cesargillao/pediluvio-ionico-zapper-pic16f876/Software/asmoutput.asm

0000: 
       GOTO   L00A2
L0001  MOVLW  80h
       MOVWF  21h
       MOVLW  0FEh
       CALL   L0061
       MOVLW  1
       CALL   L0061
       MOVLW  75h
       MOVWF  24h
       MOVLW  30h
       GOTO   L0072
L000B  CLRF   21h
       BSF    21h,7
       MOVWF  2Ch
       MOVLW  0FEh
       CALL   L0061
       MOVF   2Ch,W
       GOTO   L0061
L0012  MOVWF  2Ah
       BCF    6,2
       BCF    6,3
       BSF    3,5
       BCF    6,2
       BCF    6,3
       MOVLW  0Fh
       ANDWF  6,F
       BCF    3,5
       MOVF   2Ah,W
       BTFSC  20h,1
       GOTO   L003C
       MOVLW  3Eh
       MOVWF  24h
       MOVLW  80h
       CALL   L0072
       MOVLW  33h
       MOVWF  29h
       CALL   L0050
       MOVLW  13h
       MOVWF  24h
       MOVLW  88h
       CALL   L0072
       CALL   L0050
       MOVLW  64h
       CALL   L0071
       CALL   L0050
       MOVLW  64h
       CALL   L0071
       MOVLW  22h
       MOVWF  29h
       CALL   L0050
       MOVLW  28h
       CALL   L003B
       MOVLW  0Ch
       CALL   L003B
       MOVLW  6
       CALL   L003B
       BSF    20h,1
       MOVF   2Ah,W
       GOTO   L003C
L003B  BSF    20h,0
L003C  MOVWF  29h
       BTFSS  20h,0
       GOTO   L004A
       BCF    6,3
       SUBLW  3
       BTFSS  3,0
       GOTO   L004F
       CALL   L004F
       MOVLW  7
       MOVWF  24h
       MOVLW  0D0h
       CALL   L0072
       BSF    3,0
       RETURN
L004A  BSF    20h,0
       SUBLW  0FEh
       BTFSC  3,2
       GOTO   L005F
       BSF    6,3
L004F  BTFSS  20h,0
L0050  BCF    20h,0
       BSF    6,2
       MOVLW  0Fh
       ANDWF  6,F
       MOVF   29h,W
       ANDLW  0F0h
       IORWF  6,F
       NOP
       BCF    6,2
       SWAPF  29h,F
       NOP
       BTFSC  20h,0
       GOTO   L0050
       MOVLW  32h
       CALL   L0071
L005F  MOVF   2Ah,W
       GOTO   L009D
L0061  BTFSC  21h,7
       GOTO   L0012
       RETURN
L0064  CLRF   26h
L0065  MOVWF  25h
L0066  MOVLW  0FFh
       ADDWF  25h,F
       BTFSS  3,0
       ADDWF  26h,F
       BTFSS  3,0
       GOTO   L009D
       MOVLW  3
       MOVWF  24h
       MOVLW  0E7h
       CALL   L0072
       GOTO   L0066
L0071  CLRF   24h
L0072  ADDLW  0FCh
       MOVWF  23h
       COMF   24h,F
       BTFSS  3,0
       GOTO   L007D
L0077  MOVLW  0FFh
L0078  NOP
       ADDWF  23h,F
       BTFSC  3,0
       GOTO   L0078
       ADDWF  23h,F
L007D  NOP
       INCFSZ 24h,F
       GOTO   L0077
       RETURN
L0081  CLRF   28h
       CLRF   27h
       MOVLW  10h
       MOVWF  29h
L0085  RLF    24h,W
       RLF    27h,F
       RLF    28h,F
       MOVF   25h,W
       SUBWF  27h,F
       MOVF   26h,W
       BTFSS  3,0
       INCFSZ 26h,W
       SUBWF  28h,F
       BTFSC  3,0
       GOTO   L0097
       MOVF   25h,W
       ADDWF  27h,F
       MOVF   26h,W
       BTFSC  3,0
       INCFSZ 26h,W
       ADDWF  28h,F
       BCF    3,0
L0097  RLF    23h,F
       RLF    24h,F
       DECFSZ 29h,F
       GOTO   L0085
       MOVF   23h,W
       GOTO   L009D
L009D  BCF    3,7
       BCF    3,5
       BCF    3,6
       NOP
       RETURN
L00A2  CLRF   20h
       MOVLW  7
       MOVWF  1Fh
       MOVLW  7
       MOVWF  1Fh
       BSF    3,5
       BCF    5,3
       BCF    3,5
       BSF    5,3
       BSF    3,5
       BCF    5,2
       BCF    3,5
       BSF    5,2
       CLRF   3Ah
       CLRF   39h
       CLRF   41h
       BCF    44h,0
       CLRF   2Eh
       CLRF   2Dh
       CLRF   30h
       CLRF   2Fh
       CLRF   32h
       CLRF   31h
       MOVLW  64h
       CALL   L0064
       CALL   L0001
       MOVLW  80h
       MOVWF  21h
       MOVLW  80h
       CALL   L000B
       MOVLW  20h
       CALL   L0012
       CALL   L0012
       CALL   L0012
       MOVLW  43h
       CALL   L0012
       MOVLW  61h
       CALL   L0012
       MOVLW  70h
       CALL   L0012
       MOVLW  61h
       CALL   L0012
       MOVLW  63h
       CALL   L0012
       MOVLW  0A1h
       CALL   L0012
       MOVLW  6Dh
       CALL   L0012
       MOVLW  65h
       CALL   L0012
       MOVLW  74h
       CALL   L0012
       MOVLW  72h
       CALL   L0012
       MOVLW  6Fh
       CALL   L0012
       MOVLW  20h
       CALL   L0012
       CALL   L0012
       MOVLW  80h
       MOVWF  21h
       MOVLW  0C0h
       CALL   L000B
       MOVLW  20h
       CALL   L0012
       MOVLW  44h
       CALL   L0012
       MOVLW  69h
       CALL   L0012
       MOVLW  67h
       CALL   L0012
       MOVLW  69h
       CALL   L0012
       MOVLW  74h
       CALL   L0012
       MOVLW  61h
       CALL   L0012
       MOVLW  6Ch
       CALL   L0012
       MOVLW  20h
       CALL   L0012
       MOVLW  4Eh
       CALL   L0012
       MOVLW  65h
       CALL   L0012
       MOVLW  6Fh
       CALL   L0012
       MOVLW  54h
       CALL   L0012
       MOVLW  65h
       CALL   L0012
       MOVLW  6Fh
       CALL   L0012
       MOVLW  20h
       CALL   L0012
       MOVLW  7
       MOVWF  26h
       MOVLW  0D0h
       CALL   L0065
       MOVLW  80h
       MOVWF  21h
       MOVLW  80h
       CALL   L000B
       MOVLW  20h
       CALL   L0012
       CALL   L0012
       MOVLW  41h
       CALL   L0012
       MOVLW  6Ah
       CALL   L0012
       MOVLW  75h
       CALL   L0012
       MOVLW  73h
       CALL   L0012
       MOVLW  74h
       CALL   L0012
       MOVLW  61h
       CALL   L0012
       MOVLW  6Eh
       CALL   L0012
       MOVLW  64h
       CALL   L0012
       MOVLW  6Fh
       CALL   L0012
       MOVLW  20h
       CALL   L0012
       MOVLW  65h
       CALL   L0012
       MOVLW  6Ch
       CALL   L0012
       MOVLW  20h
       CALL   L0012
       CALL   L0012
       MOVLW  80h
       MOVWF  21h
       MOVLW  0C0h
       CALL   L000B
       MOVLW  20h
       CALL   L0012
       CALL   L0012
       CALL   L0012
       CALL   L0012
       CALL   L0012
       CALL   L0012
       MOVLW  43h
       CALL   L0012
       MOVLW  65h
       CALL   L0012
       MOVLW  72h
       CALL   L0012
       MOVLW  6Fh
       CALL   L0012
       MOVLW  20h
       CALL   L0012
       CALL   L0012
       CALL   L0012
       CALL   L0012
       CALL   L0012
       CALL   L0012
       MOVLW  3
       MOVWF  26h
       MOVLW  0E8h
       CALL   L0065
       CALL   L0168
       CALL   L0001
L0147  CLRF   42h
       CALL   L0196
       MOVF   42h,F
       BTFSS  3,2
       GOTO   L0164
       MOVF   2Eh,W
       MOVWF  30h
       MOVF   2Dh,W
       MOVWF  2Fh
       MOVLW  0Ah
       CALL   L0064
       CALL   L0196
       MOVF   2Eh,W
       MOVWF  32h
       MOVF   2Dh,W
       MOVWF  31h
       MOVLW  0Ah
       CALL   L0064
       MOVF   2Fh,W
       ADDWF  31h,W
       MOVWF  2Dh
       MOVF   30h,W
       BTFSC  3,0
       ADDLW  1
       ADDWF  32h,W
       MOVWF  2Eh
       BCF    3,0
       RRF    2Eh,F
       RRF    2Dh,F
L0164  CALL   L02F4
       MOVLW  64h
       CALL   L0064
       GOTO   L0147
L0168  CLRF   38h
       CLRF   3Eh
       CLRF   3Dh
       BSF    3,5
       BSF    6,1
       BCF    6,0
       BCF    3,5
       BSF    6,0
       CLRF   42h
L0171  MOVLW  2
       SUBWF  42h,W
       BTFSC  3,0
       GOTO   L0192
       CLRF   3Ah
       CLRF   39h
       CALL   L02CA
L0178  BTFSS  5,4
       GOTO   L0189
       INCF   39h,F
       BTFSC  3,2
       INCF   3Ah,F
       MOVLW  27h
       SUBWF  3Ah,W
       BTFSS  3,0
       GOTO   L0188
       BTFSS  3,2
       GOTO   L0187
       MOVLW  10h
       SUBWF  39h,W
       BTFSS  3,0
       GOTO   L0188
L0187  GOTO   L0168
L0188  GOTO   L0178
L0189  MOVF   39h,W
       ADDWF  3Dh,F
       MOVF   3Ah,W
       BTFSC  3,0
       ADDLW  1
       ADDWF  3Eh,F
       INCF   42h,F
       BTFSS  3,2
       GOTO   L0171
L0192  BCF    3,0
       RRF    3Eh,F
       RRF    3Dh,F
       RETURN
L0196  CLRF   2Eh
       CLRF   2Dh
       MOVF   3Eh,W
       MOVWF  3Ah
       MOVF   3Dh,W
       MOVWF  39h
       MOVLW  70h
       MOVWF  37h
       CLRF   38h
       MOVLW  0Fh
       ADDWF  3Dh,W
       MOVWF  3Bh
       MOVLW  27h
       BTFSC  3,0
       ADDLW  1
       ADDWF  3Eh,W
       MOVWF  3Ch
       BSF    3,5
       BSF    6,1
       BCF    6,0
       BCF    3,5
       BSF    6,0
       CALL   L02CA
L01AD  BTFSS  5,4
       GOTO   L01BE
       INCF   2Dh,F
       BTFSC  3,2
       INCF   2Eh,F
       MOVF   2Eh,W
       SUBWF  3Ch,W
       BTFSS  3,0
       GOTO   L01BC
       BTFSS  3,2
       GOTO   L01BD
       MOVF   2Dh,W
       SUBWF  3Bh,W
       BTFSC  3,0
       GOTO   L01BD
L01BC  GOTO   L01EC
L01BD  GOTO   L01AD
L01BE  MOVF   39h,W
       SUBWF  2Dh,F
       MOVF   3Ah,W
       BTFSS  3,0
       ADDLW  1
       SUBWF  2Eh,F
L01C4  MOVLW  27h
       SUBWF  2Eh,W
       BTFSS  3,0
       GOTO   L01D2
       BTFSS  3,2
       GOTO   L01CE
       MOVLW  10h
       SUBWF  2Dh,W
       BTFSS  3,0
       GOTO   L01D2
L01CE  INCF   2Dh,F
       BTFSC  3,2
       INCF   2Eh,F
       GOTO   L01C4
L01D2  MOVLW  3
       SUBWF  2Eh,W
       BTFSS  3,0
       GOTO   L01EB
       BTFSS  3,2
       GOTO   L01DC
       MOVLW  0E8h
       SUBWF  2Dh,W
       BTFSS  3,0
       GOTO   L01EB
L01DC  MOVF   2Eh,W
       MOVWF  24h
       MOVF   2Dh,W
       MOVWF  23h
       CLRF   26h
       MOVLW  0Ah
       MOVWF  25h
       CALL   L0081
       MOVWF  2Dh
       MOVF   24h,W
       MOVWF  2Eh
       MOVLW  6Eh
       MOVWF  37h
       MOVLW  1
       MOVWF  38h
L01EB  RETURN
L01EC  CLRF   2Eh
       CLRF   2Dh
       MOVLW  6Eh
       MOVWF  37h
       CLRF   38h
       CLRF   3Ah
       CLRF   39h
       MOVLW  1
       MOVWF  42h
       BSF    3,5
       BCF    6,1
       BCF    6,1
       BCF    3,5
       BSF    6,1
       BSF    3,5
       BCF    6,0
       BCF    3,5
       BSF    6,0
       CALL   L02CA
L01FF  BTFSS  5,4
       GOTO   L0210
       INCF   2Dh,F
       BTFSC  3,2
       INCF   2Eh,F
       MOVLW  27h
       SUBWF  2Eh,W
       BTFSS  3,0
       GOTO   L020F
       BTFSS  3,2
       GOTO   L020E
       MOVLW  10h
       SUBWF  2Dh,W
       BTFSS  3,0
       GOTO   L020F
L020E  GOTO   L022A
L020F  GOTO   L01FF
L0210  MOVLW  3
       SUBWF  2Eh,W
       BTFSS  3,0
       GOTO   L0229
       BTFSS  3,2
       GOTO   L021A
       MOVLW  0E8h
       SUBWF  2Dh,W
       BTFSS  3,0
       GOTO   L0229
L021A  MOVF   2Eh,W
       MOVWF  24h
       MOVF   2Dh,W
       MOVWF  23h
       CLRF   26h
       MOVLW  0Ah
       MOVWF  25h
       CALL   L0081
       MOVWF  2Dh
       MOVF   24h,W
       MOVWF  2Eh
       MOVLW  75h
       MOVWF  37h
       MOVLW  1
       MOVWF  38h
L0229  RETURN
L022A  CLRF   2Eh
       CLRF   2Dh
       MOVLW  1
       MOVWF  42h
       MOVLW  75h
       MOVWF  37h
       CLRF   38h
       CLRF   3Ah
       CLRF   39h
       BSF    3,5
       BSF    6,1
       BCF    6,0
       BCF    3,5
       BCF    6,0
       CALL   L02DD
       BSF    3,5
       BCF    5,2
       BCF    3,5
       BSF    5,2
       MOVLW  5
       MOVWF  26h
       MOVLW  0DCh
       CALL   L0065
       BSF    3,5
       BCF    5,2
       BCF    3,5
       BCF    5,2
       CALL   L02EC
       BSF    3,5
       BCF    5,2
       BCF    3,5
       BSF    5,2
L024A  BTFSS  5,4
       GOTO   L0262
       CLRF   3Fh
L024D  MOVLW  5Dh
       SUBWF  3Fh,W
       BTFSC  3,0
       GOTO   L0253
       INCF   3Fh,F
       GOTO   L024D
L0253  INCF   2Dh,F
       BTFSC  3,2
       INCF   2Eh,F
       MOVLW  27h
       SUBWF  2Eh,W
       BTFSS  3,0
       GOTO   L0261
       BTFSS  3,2
       GOTO   L0260
       MOVLW  10h
       SUBWF  2Dh,W
       BTFSS  3,0
       GOTO   L0261
L0260  GOTO   L027C
L0261  GOTO   L024A
L0262  MOVLW  3
       SUBWF  2Eh,W
       BTFSS  3,0
       GOTO   L027B
       BTFSS  3,2
       GOTO   L026C
       MOVLW  0E8h
       SUBWF  2Dh,W
       BTFSS  3,0
       GOTO   L027B
L026C  MOVF   2Eh,W
       MOVWF  24h
       MOVF   2Dh,W
       MOVWF  23h
       CLRF   26h
       MOVLW  0Ah
       MOVWF  25h
       CALL   L0081
       MOVWF  2Dh
       MOVF   24h,W
       MOVWF  2Eh
       MOVLW  6Dh
       MOVWF  37h
       MOVLW  1
       MOVWF  38h
L027B  RETURN
L027C  CLRF   2Eh
       CLRF   2Dh
       INCF   41h,F
       MOVLW  1
       MOVWF  42h
       MOVLW  6Dh
       MOVWF  37h
       CLRF   38h
       CLRF   3Ah
       CLRF   39h
       BSF    44h,0
       CALL   L02DD
       BSF    3,5
       BCF    5,2
       BCF    3,5
       BSF    5,2
       MOVLW  27h
       MOVWF  26h
       MOVLW  10h
       CALL   L0065
       MOVLW  27h
       MOVWF  26h
       MOVLW  10h
       CALL   L0065
       MOVLW  27h
       MOVWF  26h
       MOVLW  10h
       CALL   L0065
       MOVLW  27h
       MOVWF  26h
       MOVLW  10h
       CALL   L0065
       MOVLW  27h
       MOVWF  26h
       MOVLW  10h
       CALL   L0065
       MOVLW  27h
       MOVWF  26h
       MOVLW  10h
       CALL   L0065
       BSF    3,5
       BCF    5,2
       BCF    3,5
       BCF    5,2
       CALL   L02EC
       BSF    3,5
       BCF    5,2
       BCF    3,5
       BSF    5,2
L02AD  BTFSS  5,4
       GOTO   L02B5
       MOVLW  0B0h
       CALL   L0064
       INCF   2Dh,F
       BTFSC  3,2
       INCF   2Eh,F
       GOTO   L02AD
L02B5  CALL   L0001
       MOVLW  3
       SUBWF  2Eh,W
       BTFSS  3,0
       GOTO   L02C4
       BTFSS  3,2
       GOTO   L02C0
       MOVLW  0E8h
       SUBWF  2Dh,W
       BTFSS  3,0
       GOTO   L02C4
L02C0  MOVLW  46h
       MOVWF  37h
       MOVLW  1
       MOVWF  38h
L02C4  MOVLW  3
       SUBWF  41h,W
       BTFSS  3,2
       GOTO   L02C9
       GOTO   L02C4
L02C9  RETURN
L02CA  CLRF   2Eh
       CLRF   2Dh
       CALL   L02DD
       BSF    3,5
       BCF    5,2
       BCF    3,5
       BSF    5,2
       MOVLW  64h
       CALL   L0064
       BSF    3,5
       BCF    5,2
       BCF    3,5
       BCF    5,2
       CALL   L02EC
       BSF    3,5
       BCF    5,2
       BCF    3,5
       BSF    5,2
       RETURN
L02DD  BSF    3,5
       BCF    5,3
       BCF    3,5
       BSF    5,3
       BSF    3,5
       BCF    5,3
       BCF    3,5
       BCF    5,3
       MOVLW  1
       CALL   L0064
       BSF    3,5
       BCF    5,3
       BCF    3,5
       BSF    5,3
       RETURN
L02EC  CLRF   40h
L02ED  MOVLW  2
       SUBWF  40h,W
       BTFSC  3,0
       GOTO   L02F3
       INCF   40h,F
       GOTO   L02ED
L02F3  RETURN
L02F4  MOVLW  80h
       MOVWF  21h
       MOVLW  80h
       CALL   L000B
       MOVLW  20h
       CALL   L0012
       CALL   L0012
       CALL   L0012
       MOVLW  43h
       CALL   L0012
       MOVLW  61h
       CALL   L0012
       MOVLW  70h
       CALL   L0012
       MOVLW  61h
       CALL   L0012
       MOVLW  63h
       CALL   L0012
       MOVLW  69h
       CALL   L0012
       MOVLW  64h
       CALL   L0012
       MOVLW  61h
       CALL   L0012
       MOVLW  64h
       CALL   L0012
       MOVLW  20h
       CALL   L0012
       CALL   L0012
       CALL   L0012
       MOVLW  80h
       MOVWF  21h
       MOVLW  0C0h
       CALL   L000B
       MOVLW  20h
       CALL   L0012
       CALL   L0012
       CALL   L0012
       MOVLW  43h
       CALL   L0012
       MOVLW  20h
       CALL   L0012
       MOVLW  3Dh
       CALL   L0012
       MOVLW  80h
       MOVWF  21h
       MOVLW  0C7h
       CALL   L000B
       CLRF   33h
       CLRF   34h
       CLRF   35h
       CLRF   36h
L0328  MOVLW  3
       SUBWF  2Eh,W
       BTFSS  3,0
       GOTO   L033A
       BTFSS  3,2
       GOTO   L0332
       MOVLW  0E8h
       SUBWF  2Dh,W
       BTFSS  3,0
       GOTO   L033A
L0332  INCF   33h,F
       MOVLW  0E8h
       SUBWF  2Dh,F
       MOVLW  3
       BTFSS  3,0
       ADDLW  1
       SUBWF  2Eh,F
       GOTO   L0328
L033A  MOVF   33h,F
       BTFSS  3,2
       GOTO   L033F
       MOVF   33h,F
       GOTO   L0343
L033F  MOVLW  30h
       ADDWF  33h,F
       MOVF   33h,W
       CALL   L0012
L0343  MOVF   2Eh,F
       BTFSS  3,2
       GOTO   L034A
       MOVLW  64h
       SUBWF  2Dh,W
       BTFSS  3,0
       GOTO   L0350
L034A  INCF   34h,F
       MOVLW  64h
       SUBWF  2Dh,F
       BTFSS  3,0
       DECF   2Eh,F
       GOTO   L0343
L0350  MOVF   33h,W
       ADDWF  34h,W
       MOVWF  43h
       MOVF   43h,F
       BTFSS  3,2
       GOTO   L0359
       MOVLW  20h
       CALL   L0012
       GOTO   L035D
L0359  MOVLW  30h
       ADDWF  34h,F
       MOVF   34h,W
       CALL   L0012
L035D  MOVLW  1
       SUBWF  38h,W
       BTFSS  3,2
       GOTO   L0363
       MOVLW  2Eh
       CALL   L0012
L0363  MOVF   2Eh,F
       BTFSS  3,2
       GOTO   L036A
       MOVLW  0Ah
       SUBWF  2Dh,W
       BTFSS  3,0
       GOTO   L0370
L036A  INCF   35h,F
       MOVLW  0Ah
       SUBWF  2Dh,F
       BTFSS  3,0
       DECF   2Eh,F
       GOTO   L0363
L0370  MOVF   34h,W
       ADDWF  35h,W
       MOVWF  43h
       MOVF   33h,W
       ADDWF  43h,F
       MOVF   43h,F
       BTFSS  3,2
       GOTO   L037B
       MOVLW  20h
       CALL   L0012
       GOTO   L037F
L037B  MOVLW  30h
       ADDWF  35h,F
       MOVF   35h,W
       CALL   L0012
L037F  MOVF   2Dh,W
       MOVWF  36h
       MOVLW  30h
       ADDWF  36h,F
       MOVF   36h,W
       CALL   L0012
       MOVF   37h,W
       CALL   L0012
       MOVLW  46h
       CALL   L0012
       MOVLW  20h
       CALL   L0012
       CALL   L0012
       CALL   L0012
       RETURN
2007: 3F22
